speedypotato/SDVX-Panel-Conversion/CAD/sdvx_ac/box/box_3mf/back_mount.3MF

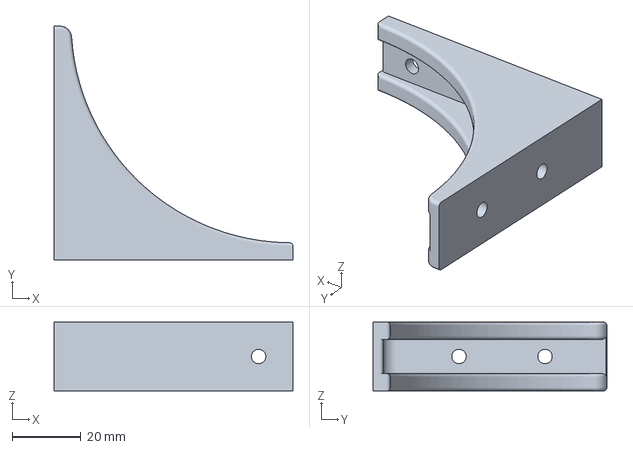
[picture p17: CAD file, 2022-09-24]
CAD/sdvx_ac/box/box_3mf/back_mount.3MF
69.5 x 68.0 x 20.0 mm
