speedypotato/SDVX-Panel-Conversion/CAD/sdvx_ac/box/side.SLDPRT

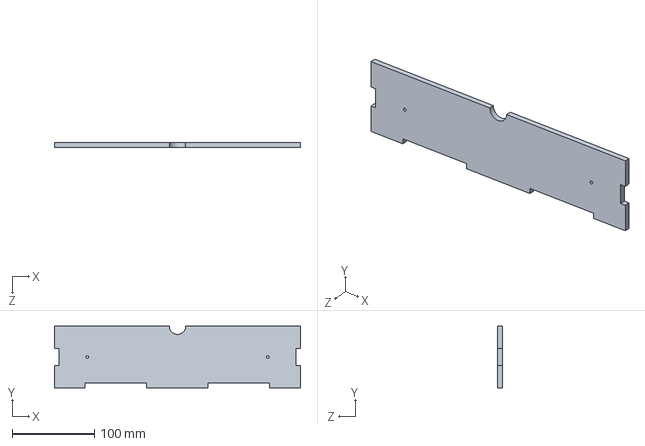
[picture p18: CAD file, 2023-04-07]
CAD/sdvx_ac/box/side.SLDPRT
300.0 x 75.0 x 5.50 mm
