speedypotato/SDVX-Panel-Conversion/CAD/sdvx_ac/box/corner_bracket.SLDPRT

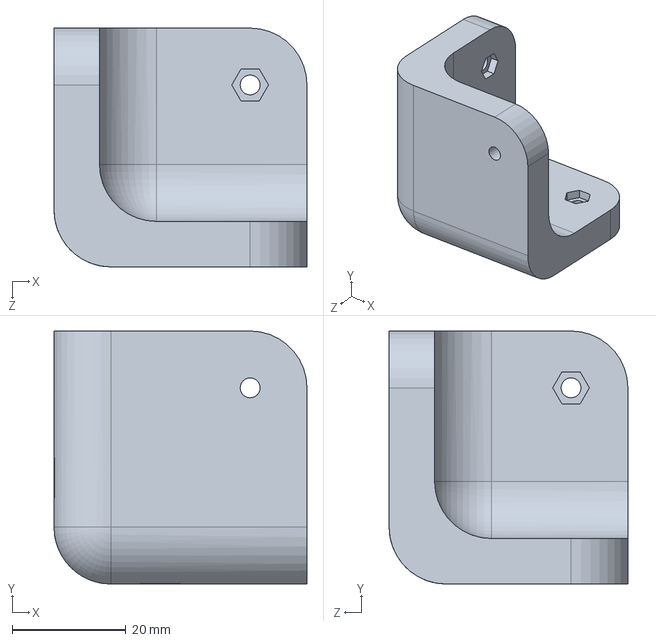
[picture p19: CAD file, 2022-09-24]
CAD/sdvx_ac/box/corner_bracket.SLDPRT
44.5 x 44.5 x 42.0 mm
