speedypotato/SDVX-Panel-Conversion/CAD/sdvx_ac/box/panel.SLDPRT

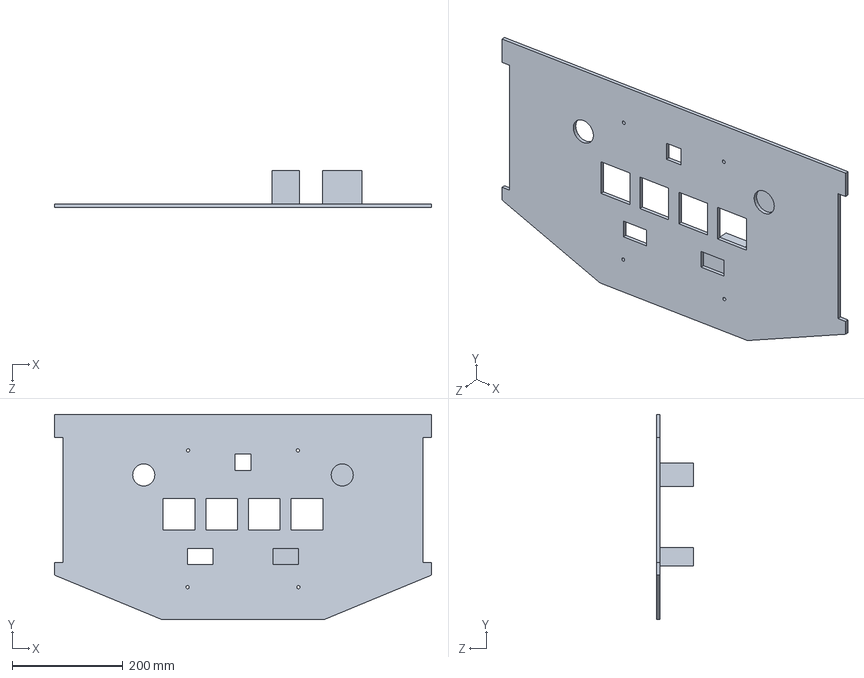
[picture p20: CAD file, 2022-09-24]
CAD/sdvx_ac/box/panel.SLDPRT
680.0 x 370.4 x 66.2 mm
