speedypotato/SDVX-Panel-Conversion/CAD/sdvx_ac/box/box.dxf

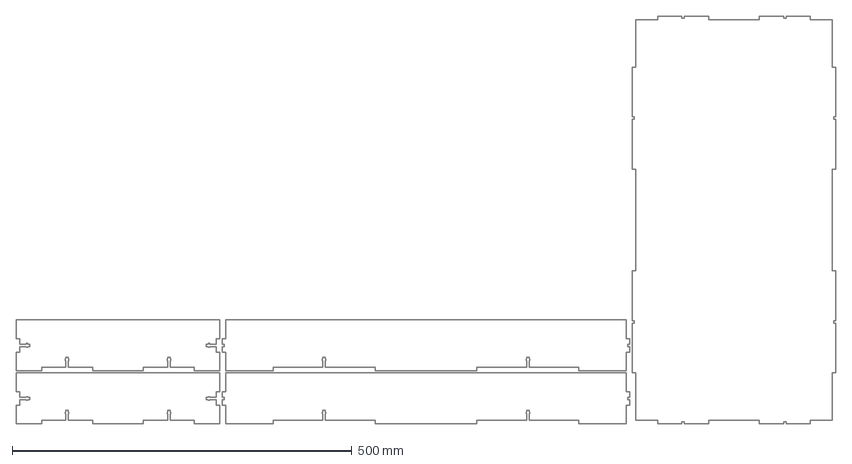
[picture p21: CAD file, 2022-09-24]
CAD/sdvx_ac/box/box.dxf
1206.0 x 600.0 mm
