speedypotato/SDVX-Panel-Conversion/CAD/sdvx_ac/box/acrylic_panel.dxf

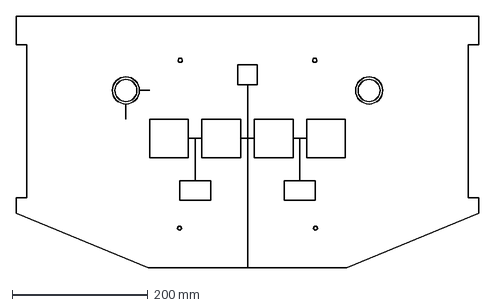
[picture p22: CAD file, 2022-08-20]
CAD/sdvx_ac/box/acrylic_panel.dxf
680.0 x 370.4 mm
